daniel-starke/vkvm/hw/seeedstudio-panel/ser-combined-bottom.png

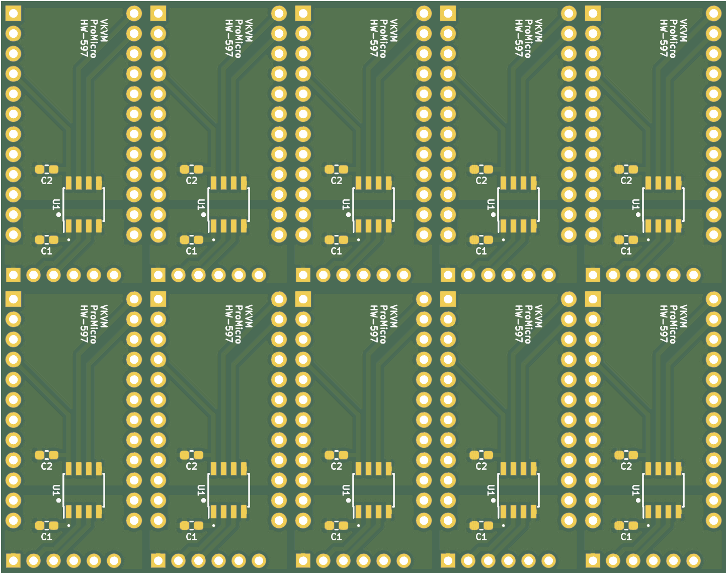
hw/seeedstudio-panel/ser-combined-bottom.png
