daniel-starke/vkvm/hw/seeedstudio-panel/ser-combined-top.png

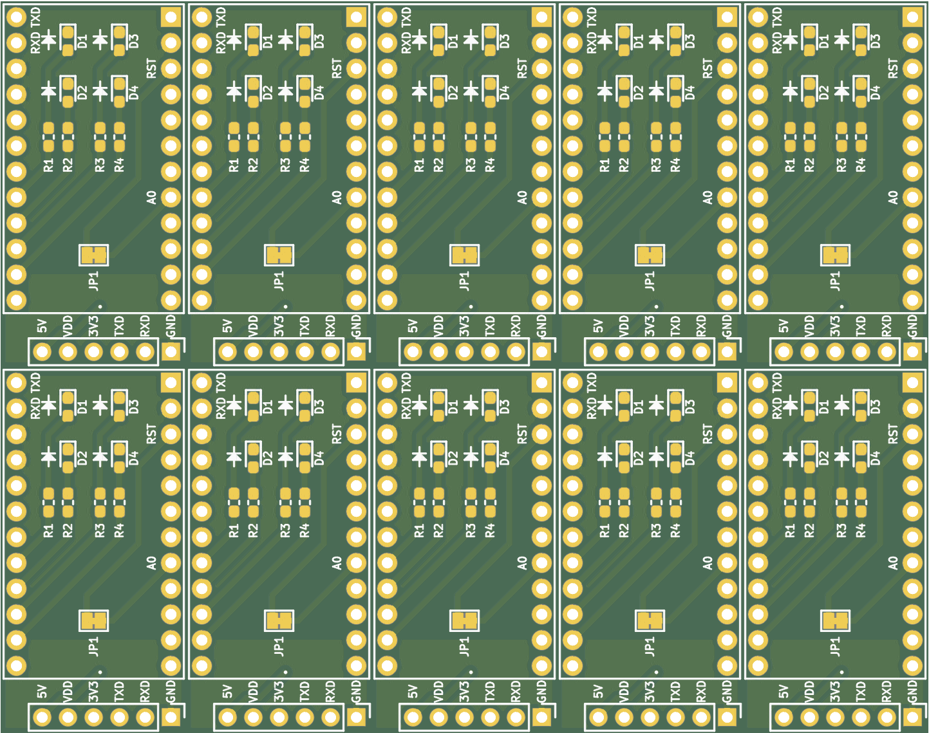
hw/seeedstudio-panel/ser-combined-top.png
