daniel-starke/vkvm/src/vkm-b/board.cpp

/**
 * @file board.cpp
 * @author Daniel Starke
 * @copyright Copyright 2020-2022 Daniel Starke
 * @date 2020-05-10
 * @version 2022-04-18
 */
#include <Arduino.h>
#include <wiring_irq.h>


/* exported variables */
HardwareSerial Serial1(USART2, getIrqNumFor(USART2), PA_3, PA_2, GPIO_AF1_USART2, GPIO_AF1_USART2);


/**
 * Initializes this board by configuring the system clock base.
 */
void initVariant() {
	RCC_OscInitTypeDef RCC_OscInitStruct = {0};
	RCC_ClkInitTypeDef RCC_ClkInitStruct = {0};
	RCC_PeriphCLKInitTypeDef PeriphClkInit = {0};
	RCC_CRSInitTypeDef RCC_CRSInitStruct = {0};

	/* Initializes the RCC Oscillators according to the specified parameters in the RCC_OscInitTypeDef structure. */
	RCC_OscInitStruct.OscillatorType = RCC_OSCILLATORTYPE_HSI48;
	RCC_OscInitStruct.HSI48State = RCC_HSI48_ON;
	RCC_OscInitStruct.PLL.PLLState = RCC_PLL_NONE;
	if (HAL_RCC_OscConfig(&RCC_OscInitStruct) != HAL_OK) {
		systemErrorHandler();
	}
	/* Initializes the CPU, AHB and APB buses clocks */
	RCC_ClkInitStruct.ClockType = RCC_CLOCKTYPE_HCLK|RCC_CLOCKTYPE_SYSCLK|RCC_CLOCKTYPE_PCLK1;
	RCC_ClkInitStruct.SYSCLKSource = RCC_SYSCLKSOURCE_HSI48;
	RCC_ClkInitStruct.AHBCLKDivider = RCC_SYSCLK_DIV1;
	RCC_ClkInitStruct.APB1CLKDivider = RCC_HCLK_DIV1;
	if (HAL_RCC_ClockConfig(&RCC_ClkInitStruct, FLASH_LATENCY_1) != HAL_OK) {
		systemErrorHandler();
	}
	PeriphClkInit.PeriphClockSelection = RCC_PERIPHCLK_USB;
	PeriphClkInit.UsbClockSelection = RCC_USBCLKSOURCE_HSI48;
	if (HAL_RCCEx_PeriphCLKConfig(&PeriphClkInit) != HAL_OK) {
		systemErrorHandler();
	}
	/* Enable the SYSCFG APB clock */
	__HAL_RCC_CRS_CLK_ENABLE();
	/* Configures CRS */
	RCC_CRSInitStruct.Prescaler = RCC_CRS_SYNC_DIV1;
	RCC_CRSInitStruct.Source = RCC_CRS_SYNC_SOURCE_USB;
	RCC_CRSInitStruct.Polarity = RCC_CRS_SYNC_POLARITY_RISING;
	RCC_CRSInitStruct.ReloadValue = __HAL_RCC_CRS_RELOADVALUE_CALCULATE(48000000, 1000);
	RCC_CRSInitStruct.ErrorLimitValue = 34;
	RCC_CRSInitStruct.HSI48CalibrationValue = 32;
	HAL_RCCEx_CRSConfig(&RCC_CRSInitStruct);
}
